donundeen/WeCanMusic/arduino/RPiCompatible/wecanmusic_capacitive/wecanmusic_device_specific_capacitive.ino

//////////////////////////////
// DEVICE-SPECIFIC CONFIG VARS
// MULTIVALUE SETUP
const int DEVICE_NUM_MULTIVALUES = 1;

// sensor config vars - pins
// Just test touch pin - Touch0 is T0 which is on GPIO 4.
// using 32 - This is GPIO #32 and also an analog input A7 on ADC #1
int inputPin[] = {T9,T6,T8,T4, T5, T7}; //15;
//int inputPin[] = {T0, T6, T9,T8,T4, T5}; //15;
//int inputPin[] = {T4, T6, T9,T8,T4, T5}; //15;
// t9 is pin 32
// T0 is A5

// END DEVICE-SPECIFIC CONFIG VARS
//////////////////////////////


////////////////////////////////////////////////////
/////////////////////////////
// DEVICE SPECIFIC FUNCTIONS
void sensor_setup_device(){
  // nothing device-specific to do here
}

// sensor_loop must:
// - set ADCRaw[vindex] with the read sensor value
// - set firstSense[vindex] to true
void sensor_loop(int vindex){
  // use capacative inputPin
  ADCRaw[vindex] = touchRead(inputPin[vindex]);
  //ADCRaw = analogRead(sensorPin);

  //Serial.println("read value");
  //Serial.println(ADCRaw[vindex]);

  firstSense[vindex] = true;   
  /*
  if(!no_network){
    sendOSCUDP(ADCRaw);
  }
  */
  // should be 10
  //delay(10); // removing when using timeouts
}
// END DEVICE SPECIFIC FUNCTIONS
/////////////////////////////



int get_num_multivalues(){
    return DEVICE_NUM_MULTIVALUES;
}
