donundeen/WeCanMusic/arduino/RPiCompatible/wecanmusic_colorsensor/networking_functions.ino

////////////////////////////////
// NETWORKING FUNCTIONS
void network_setup() {

  delay(1000);
  Serial.println("setup");

  // for incoming UDP
//  SLIPSerial.begin(115200);
  pinMode(21, INPUT_PULLUP);

  pinMode(BUILTIN_LED, OUTPUT);

  Serial.print("ESP Board MAC Address:  ");
  Serial.println(WiFi.macAddress());

  thisarduinomac = WiFi.macAddress();

  if(WIFI_MODE_ON){
 
      // wifi config business

    if(HARDCODE_SSID){
      Serial.println("connecting to hardcoded SSID");
      Serial.println(WIFI_SSID);
      Serial.println(WIFI_PASSWORD);
      
      WiFi.begin(WIFI_SSID, WIFI_PASSWORD);
      while (WiFi.status() != WL_CONNECTED) {
        // wifi status codes: https://realglitch.com/2018/07/arduino-wifi-status-codes/
        delay(1000);
        Serial.print(".");
        Serial.print(WiFi.status());
        if(WiFi.status() == WL_CONNECTED){
          Serial.print("WL_CONNECTED");
        }
        if(WiFi.status() == WL_IDLE_STATUS){
          Serial.print("WL_IDLE_STATUS");
        }
        if(WiFi.status() == WL_CONNECT_FAILED){
          Serial.print("WL_CONNECT_FAILED");
        }
        if(WiFi.status() == WL_NO_SSID_AVAIL){
          Serial.print("WL_NO_SSID_AVAIL");
        }
        if(WiFi.status() == WL_SCAN_COMPLETED){
          Serial.print("WL_SCAN_COMPLETED");
        }
        if(WiFi.status() == WL_CONNECT_FAILED){
          Serial.print("WL_CONNECT_FAILED");
        }
        if(WiFi.status() == WL_CONNECTION_LOST){
          Serial.print("WL_CONNECTION_LOST");
        }
        if(WiFi.status() == WL_DISCONNECTED){
          Serial.print("WL_DISCONNECTED");
        }
      }
    }else{
      config_webpage_setup();
    }
  }
}


void network_loop(){

  if(!HARDCODE_SSID){
   // Portal.handleClient();
  }
  configUdp();
}



/*
 * connecting to UDP port on laptop runnin Max (or otherwise sending/recieving UDP data)
 */
void configUdp(){
  if(WIFI_MODE_ON){
    if(!wifi_connected && WiFi.status() == WL_CONNECTED){
      Serial.println("HTTP server:" + WiFi.localIP().toString());
      thisarduinoip = WiFi.localIP().toString();
      Serial.println("SSID:" + WiFi.SSID());
      wifi_connected = true;
      udp.begin(UDPINPort);
    }
    if(WiFi.status() != WL_CONNECTED){
      Serial.println("wifi not connected");
      wifi_connected = false;
    }
  }
}


///////////////////////////////
// functions to handle communication with the server/conductor

void announceCreation(){
  for(int i=0; i< NUM_MULTIVALUES; i++){
    announceCreation(i);
  }
}
// send announce message over OSC when connected
void announceCreation(int vindex){
  if(WiFi.status() == WL_CONNECTED){   
    Serial.println("ANNOUNCING udp:::");
    Serial.println(UDPReceiverIP);
    Serial.println(UDPPort);
    Serial.println(DEVICE_NAME[vindex]);  //MULTIVALUE UPDATE REQUIRED
    Serial.println(midi_bank[vindex]);  //MULTIVALUE UPDATE REQUIRED
    Serial.println(midi_bank[vindex]);  //MULTIVALUE UPDATE REQUIRED
    //send hello world to server
    char ipbuffer[20];
    thisarduinoip.toCharArray(ipbuffer, 20);
    Serial.println(ipbuffer);
    OSCMessage oscmsg("/announceUDPInstrument");  
    oscmsg.add(DEVICE_NAME[vindex]).add(midi_bank[vindex]).add(midi_program[vindex]).add(midimin[vindex]).add(midimax[vindex]);  //MULTIVALUE UPDATE REQUIRED
 //   udp.beginPacket(UDPReceiverIP, UDPPort);
    udp.beginPacket(UDPReceiverIP, 7005); // this needs to get set in a config somehwere...
 
   // udp.beginMulticastPacket(UDPReceiverIP, UDPPort, WiFi.localIP());
  //  udp.write(buffer, msg.length()+1);
    oscmsg.send(udp);
    udp.endPacket();
    oscmsg.empty();
  }else{
    Serial.println("not sending udp, not connected");
  }  
}

// send a makeNote to the server (use this when device doesn't have its own speakers or synth)
void sendMakeNote(int vindex, int pitch, int velocity, int duration){  //MULTIVALUE UPDATE REQUIRED
  if(velocity == 0){
    // don't send if value is 0
    return;
  }
  OSCMessage oscmsg("/makeNote");  
  oscmsg.add(DEVICE_NAME[vindex]).add(pitch).add(velocity).add(duration);  //MULTIVALUE UPDATE REQUIRED
  //   udp.beginPacket(UDPReceiverIP, UDPPort);
  udp.beginPacket(UDPReceiverIP, 7005); // this needs to get set in a config somehwere...

  // udp.beginMulticastPacket(UDPReceiverIP, UDPPort, WiFi.localIP());
  //  udp.write(buffer, msg.length()+1);
  oscmsg.send(udp);
  udp.endPacket();
  oscmsg.empty();  
}





// END NETWORKING FUNCTIONS
////////////////////////////////
