donundeen/WeCanMusic/arduino/Streamlined/common_headers/timing_functions.h

//////////////////////////
// TIMING FUNCTIONS
void clock_setup(){
    // avaliable resolutions
  // [ uClock.PPQN_24, uClock.PPQN_48, uClock.PPQN_96, uClock.PPQN_384, uClock.PPQN_480, uClock.PPQN_960 ]
  // not mandatory to call, the default is 96PPQN if not set

  // 2024-07-15: I don't this we use the clock, let's comment this out:
  /*
  uClock.init();  
  uClock.setPPQN(PPQNr);
  uClock.setOnPPQN(onPPQNCallback);
  uClock.setOnClockStart(onClockStartCallback);
  uClock.setTempo(bpm);
  uClock.start();
  */
}

void onPPQNCallback(uint32_t tick) {
} 

void onClockStartCallback(){
  Serial.println("clock start");
}
// END TIMING FUNCTIONS
//////////////////////////
